RyanBLeon28/Estacao-Meteorologica/Imagens/comunicando.jpeg

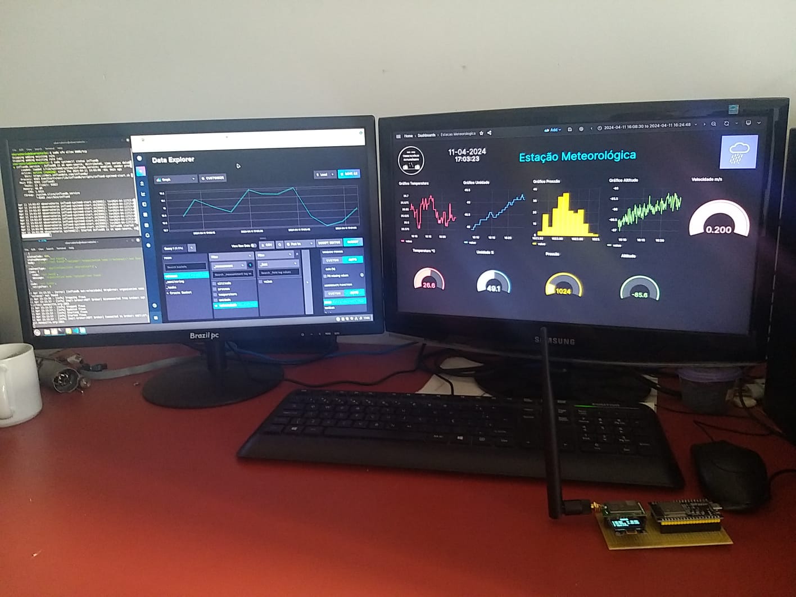
Imagens/comunicando.jpeg
