RyanBLeon28/Estacao-Meteorologica/Imagens/corrigirInfluxDB.png

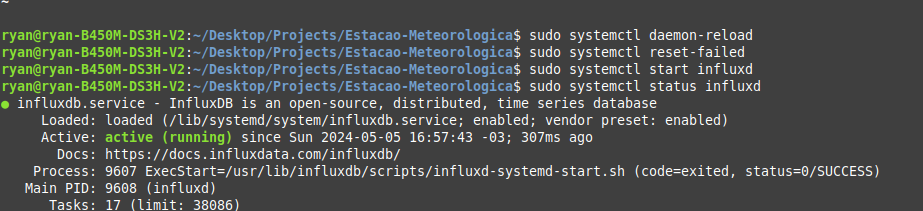
Imagens/corrigirInfluxDB.png
