RyanBLeon28/Estacao-Meteorologica/Imagens/dashboardGrafana.PNG

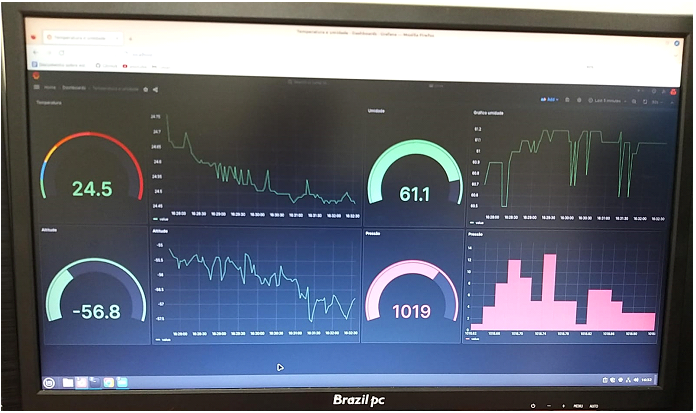
Imagens/dashboardGrafana.PNG
