RyanBLeon28/Estacao-Meteorologica/Imagens/dashboardNode.png

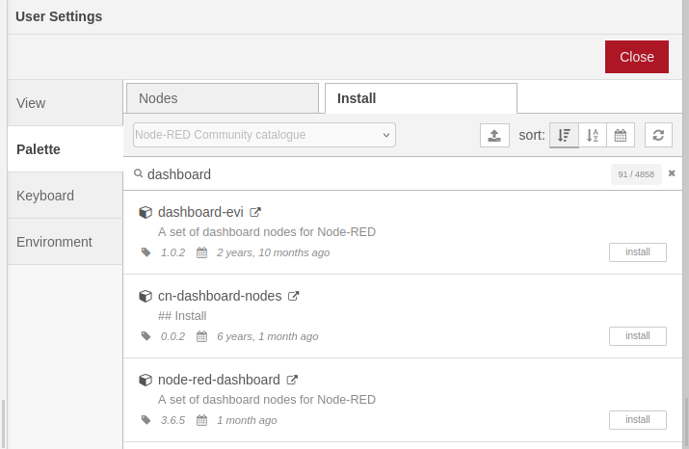
Imagens/dashboardNode.png
