RyanBLeon28/Estacao-Meteorologica/Imagens/dashboardNodeRed2.jpeg

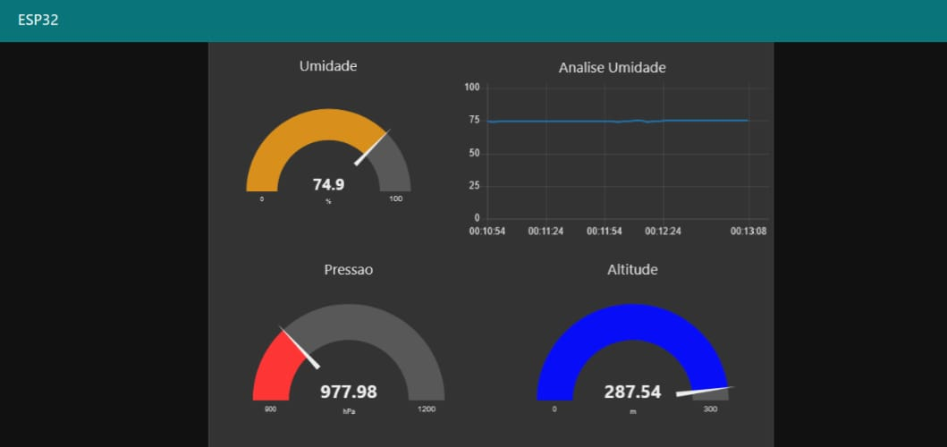
Imagens/dashboardNodeRed2.jpeg
