RyanBLeon28/Estacao-Meteorologica/Imagens/dashboardNodeRed-Influxdb-Grafana.jpeg

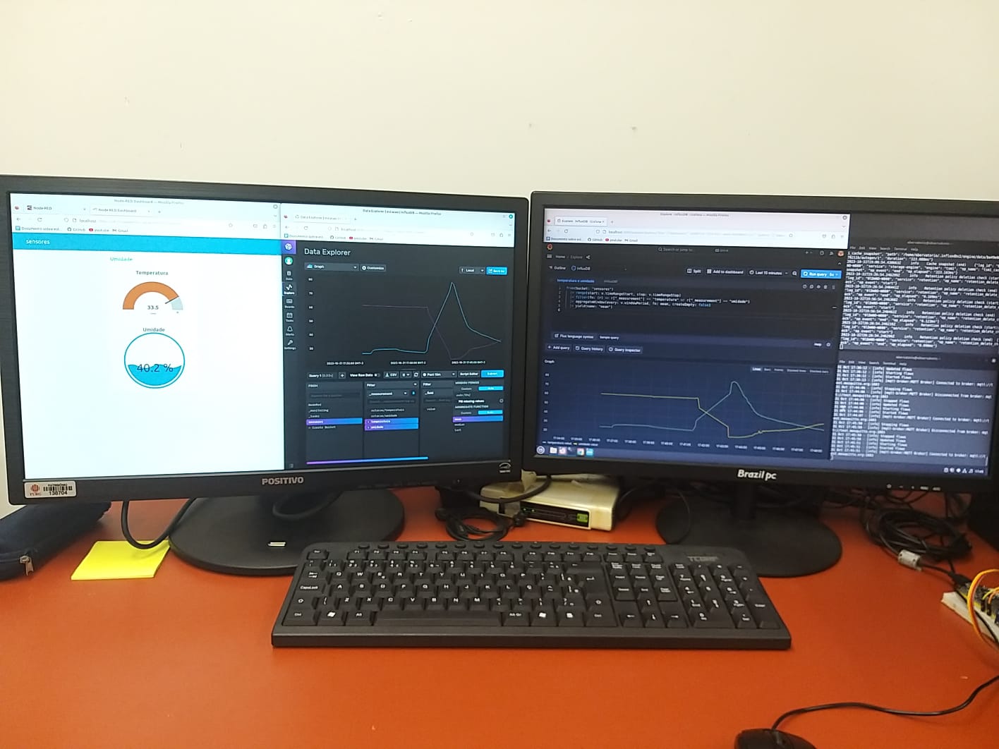
Imagens/dashboardNodeRed-Influxdb-Grafana.jpeg
