RyanBLeon28/Estacao-Meteorologica/Imagens/dashboardNodeRed.jpeg

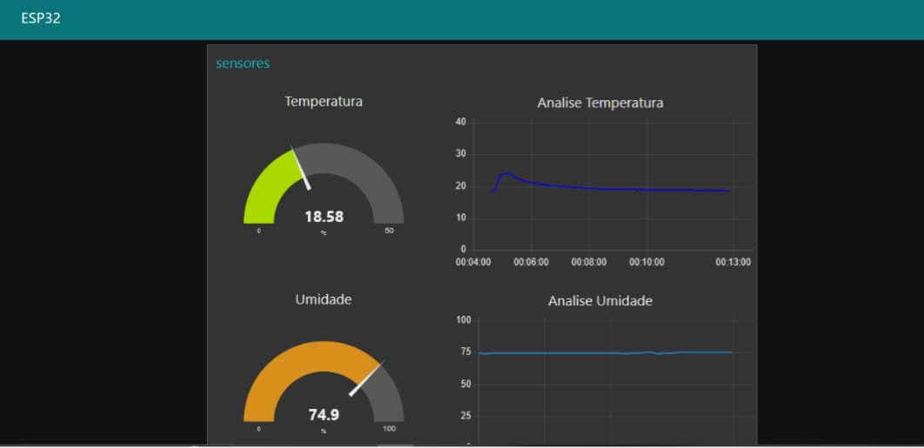
Imagens/dashboardNodeRed.jpeg
