RyanBLeon28/Estacao-Meteorologica/Imagens/dashboardNodeRed.PNG

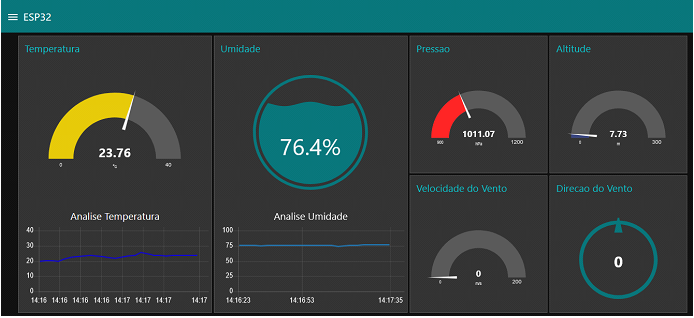
Imagens/dashboardNodeRed.PNG
