RyanBLeon28/Estacao-Meteorologica/Imagens/estacaoIni.jpeg

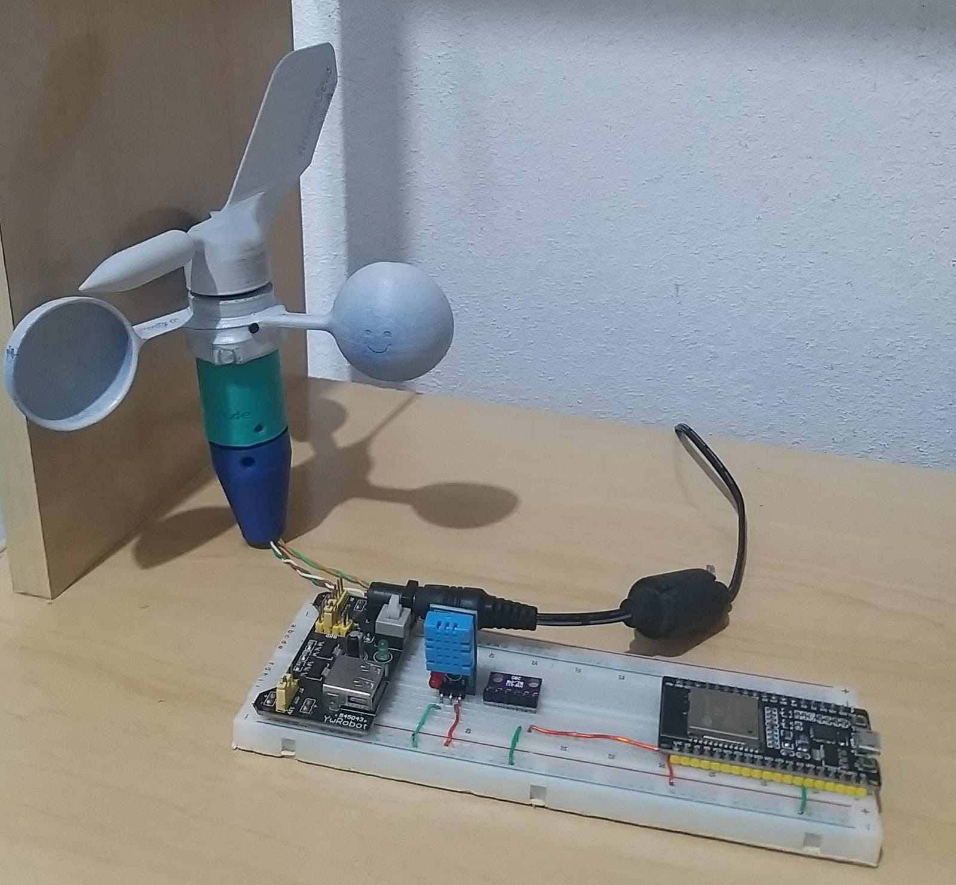
Imagens/estacaoIni.jpeg
