RyanBLeon28/Estacao-Meteorologica/Imagens/Estacaoo.jpeg

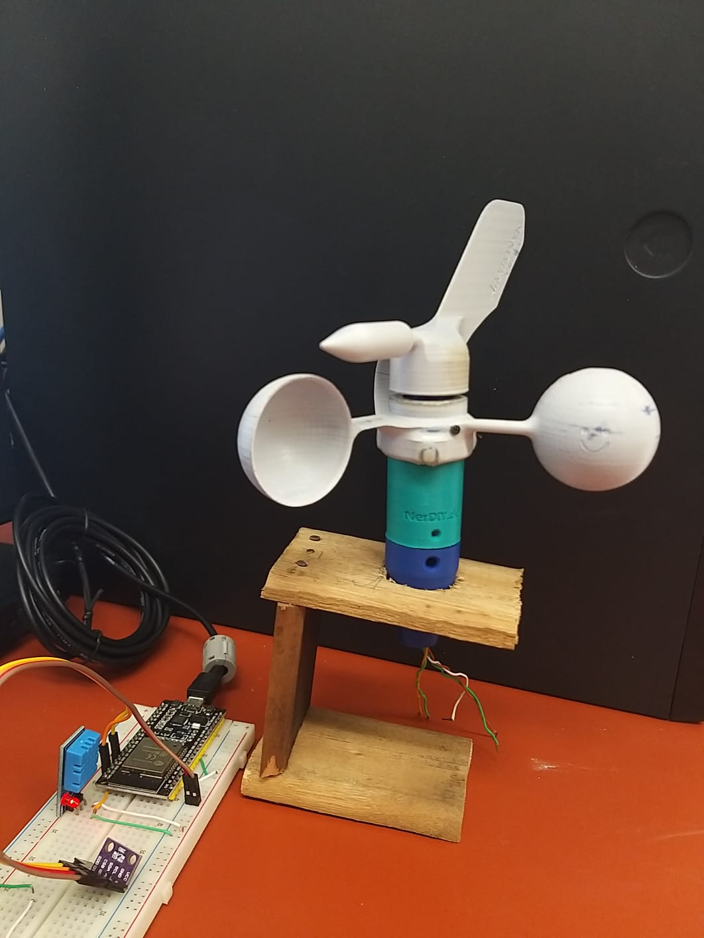
Imagens/Estacaoo.jpeg
