RyanBLeon28/Estacao-Meteorologica/Imagens/influxdbNode.png

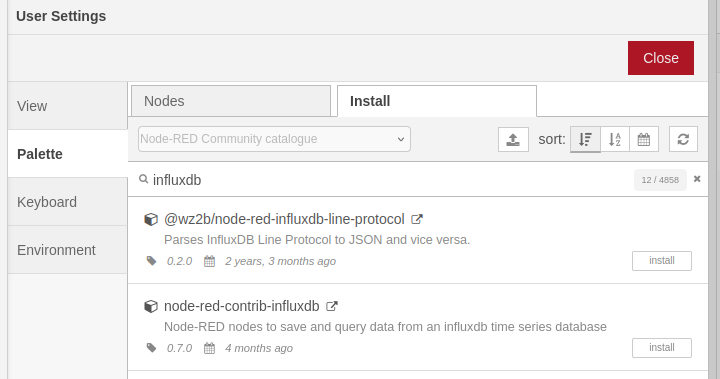
Imagens/influxdbNode.png
