RyanBLeon28/Estacao-Meteorologica/Imagens/SensorHall.jpeg

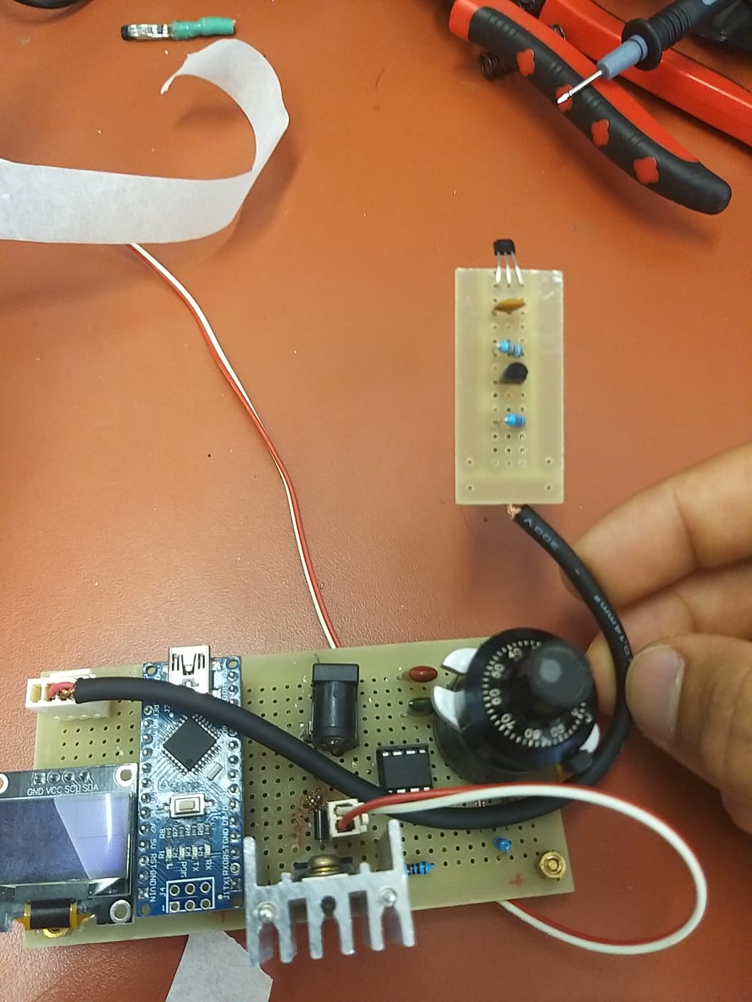
Imagens/SensorHall.jpeg
