RyanBLeon28/Estacao-Meteorologica/Imagens/serialMonitorESPtoMQTT.PNG

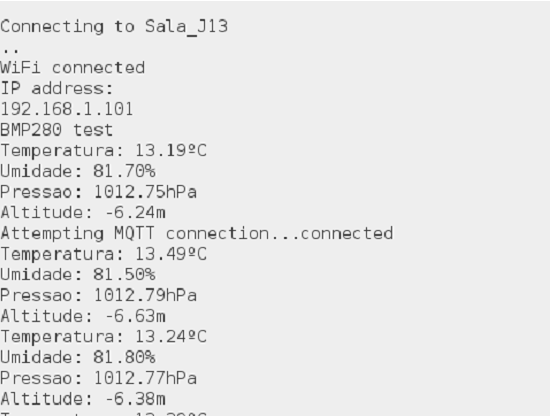
Imagens/serialMonitorESPtoMQTT.PNG
