RyanBLeon28/Estacao-Meteorologica/Imagens/servidorLocalESP32.PNG

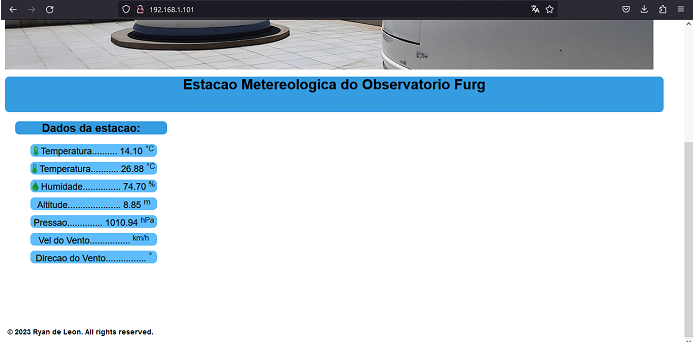
Imagens/servidorLocalESP32.PNG
