RyanBLeon28/Estacao-Meteorologica/Anemometro/Imagens da Calibracao/esqmGerencDados.PNG

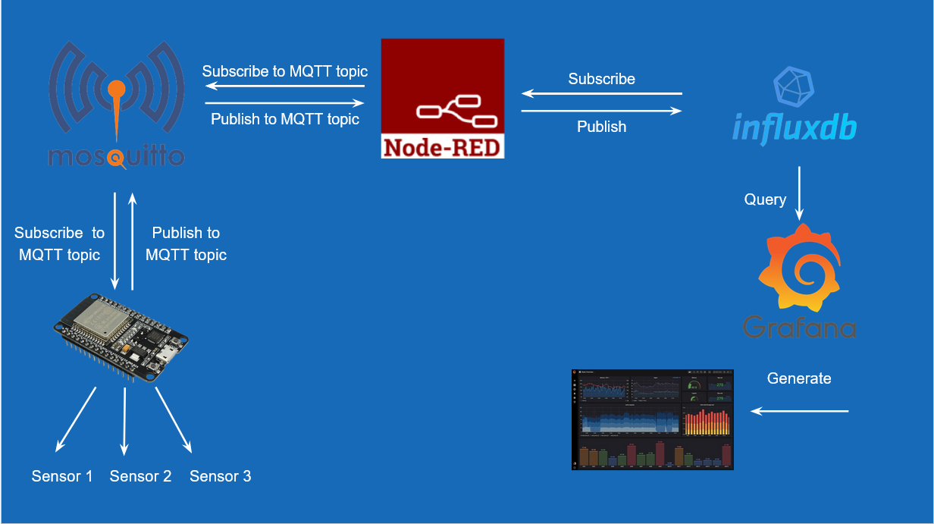
Anemometro/Imagens da Calibracao/esqmGerencDados.PNG
