RyanBLeon28/Estacao-Meteorologica/Anemometro/Imagens da Calibracao/Resultado de 120 amostras.jpeg

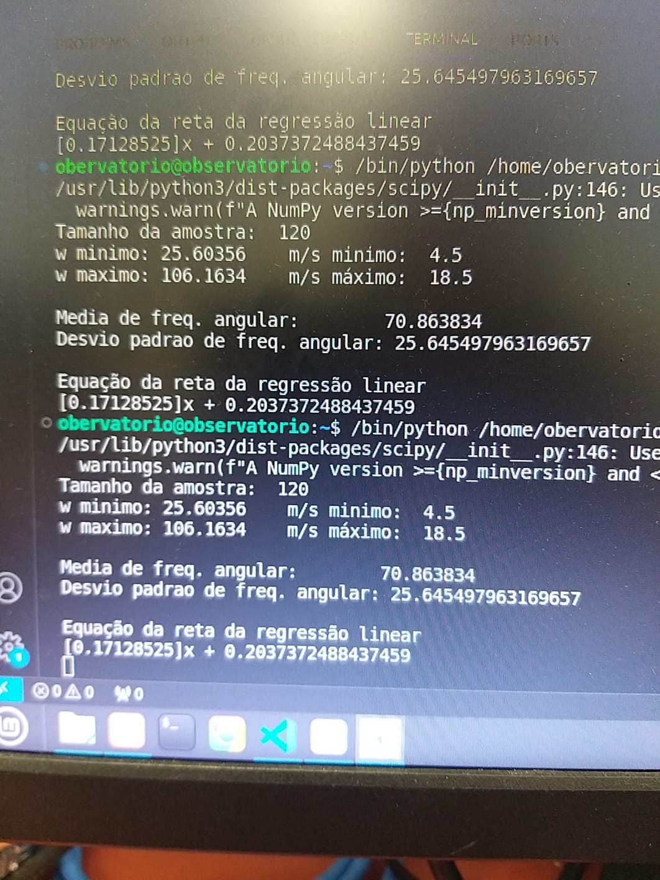
Anemometro/Imagens da Calibracao/Resultado de 120 amostras.jpeg
