RyanBLeon28/Estacao-Meteorologica/Lora/ESP_Arduino/ReceiverUNO/ReceiverUNO.ino

/*

  This example shows how to connect to an EBYTE transceiver
  using an Arduino Nano

  This code for for the sender


  connections
  Module      Arduino
  M0          4
  M1          5
  Rx          2 (This is the MCU Tx lined)
  Tx          3 (This is the MCU Rx line)
  Aux         6
  Vcc         3V3
  Gnd         Gnd

*/

#include <SoftwareSerial.h>
#include "EBYTE.h"

#define PIN_RX 2
#define PIN_TX 3
#define PIN_M0 4
#define PIN_M1 5
#define PIN_AX 6


// i recommend putting this code in a .h file and including it
// from both the receiver and sender modules
struct DATA {
  unsigned long Count;
  int Bits;
  float Volts;
  float Amps;

};

// these are just dummy variables, replace with your own
int Chan;
DATA MyData;
unsigned long Last;

// connect to any digital pin to connect to the serial port
// don't use pin 01 and 1 as they are reserved for USB communications
SoftwareSerial ESerial(PIN_RX, PIN_TX);

// create the transceiver object, passing in the serial and pins
EBYTE Transceiver(&ESerial, PIN_M0, PIN_M1, PIN_AX);
float temp;
void setup() {


  Serial.begin(9600);

  ESerial.begin(9600);
  Serial.println("Starting Reader");

  // this init will set the pinModes for you
  Transceiver.init();

  // all these calls are optional but shown to give examples of what you can do

  // Serial.println(Transceiver.GetAirDataRate());
  // Serial.println(Transceiver.GetChannel());

  // Transceiver.SetAddressH(1);
  // Transceiver.SetAddressL(0);
  // Chan = 5;
  // Transceiver.SetChannel(Chan);
  // save the parameters to the unit,
  // Transceiver.SaveParameters(PERMANENT);

  // you can print all parameters and is good for debugging
  // if your units will not communicate, print the parameters
  // for both sender and receiver and make sure air rates, channel
  // and address is the same
  Transceiver.PrintParameters();


}

void loop() {

  // if the transceiver serial is available, proces incoming data
  // you can also use Transceiver.available()


  if (ESerial.available()) {

    // i highly suggest you send data using structures and not
    // a parsed data--i've always had a hard time getting reliable data using
    // a parsing method

    Transceiver.GetStruct(&temp, sizeof(temp));
  // You only really need this library to program these EBYTE units. 
  // For reading data structures, you can call readBytes directly on the EBYTE Serial object
  // ESerial.readBytes((uint8_t*)& MyData, (uint8_t) sizeof(MyData));
  
    // dump out what was just received
    // Serial.print("Count: "); Serial.println(MyData.Count);
    // Serial.print("Bits: "); Serial.println(MyData.Bits);
    // Serial.print("Volts: "); Serial.println(MyData.Volts);
    Serial.print("Temp: ");
    Serial.println(temp);
    // if you got data, update the checker
    Last = millis();

  }
  else {
    // if the time checker is over some prescribed amount
    // let the user know there is no incoming data
    if ((millis() - Last) > 1000) {
      Serial.println("Searching: ");
      Last = millis();
    }

  }
}
